himikat123/Simple-Clock-BIM32/Solidworks2023/buttons.png

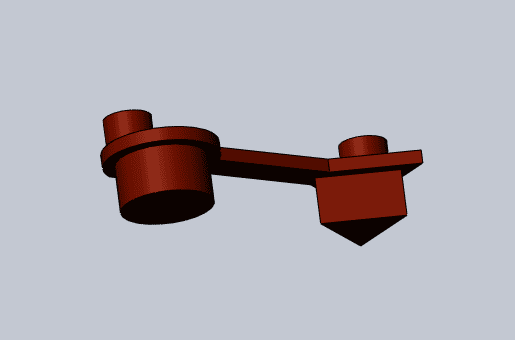
Solidworks2023/buttons.png
