himikat123/Simple-Clock-BIM32/Solidworks2023/cover.png

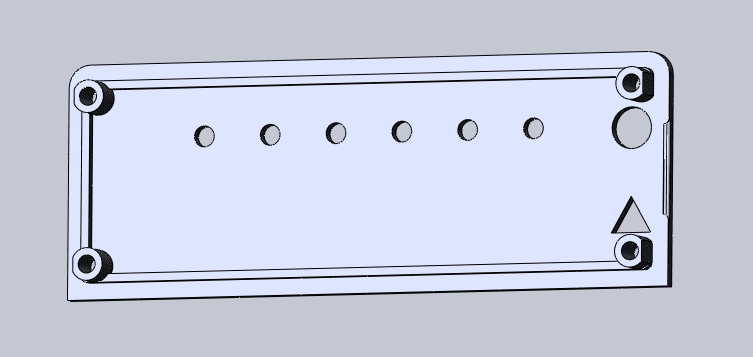
Solidworks2023/cover.png
