himikat123/Simple-Clock-BIM32/Solidworks2023/face.png

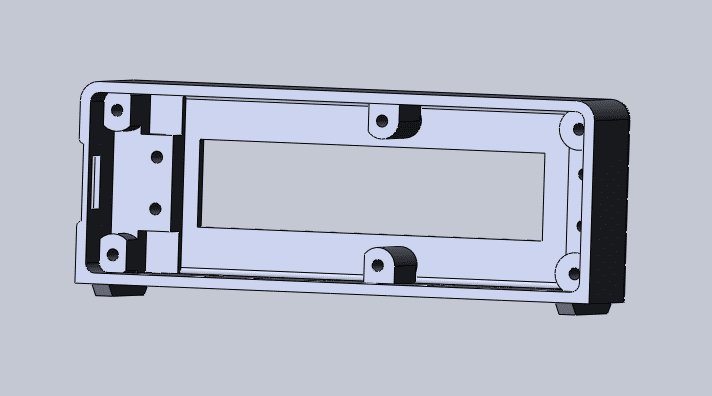
Solidworks2023/face.png
