himikat123/Simple-Clock-BIM32/STL/buttons.png

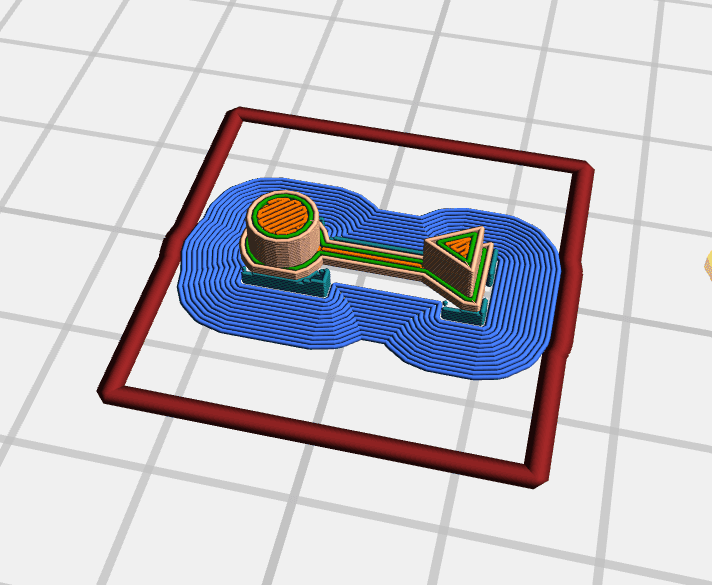
STL/buttons.png
