himikat123/Simple-Clock-BIM32/STL/cover.png

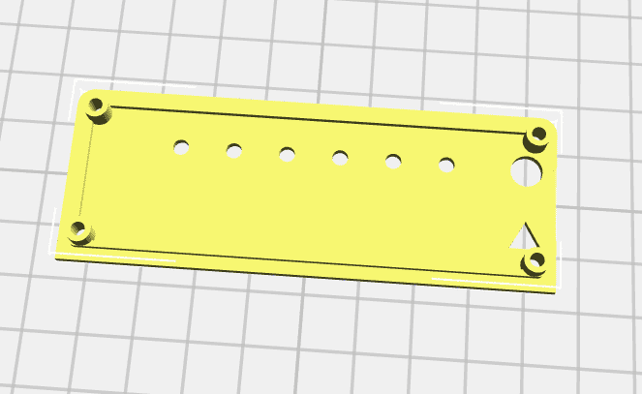
STL/cover.png
