himikat123/Simple-Clock-BIM32/STL/face.png

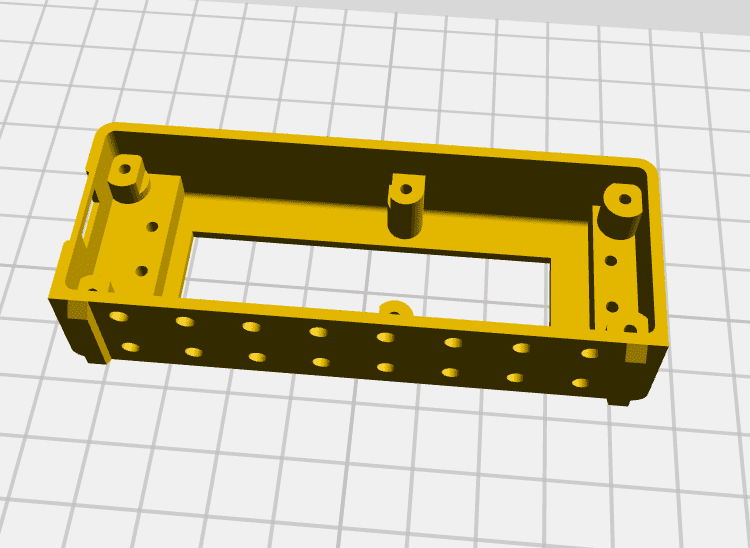
STL/face.png
