himikat123/Simple-Clock-BIM32/Solidworks2023/node mcu/esp1.SLDPRT

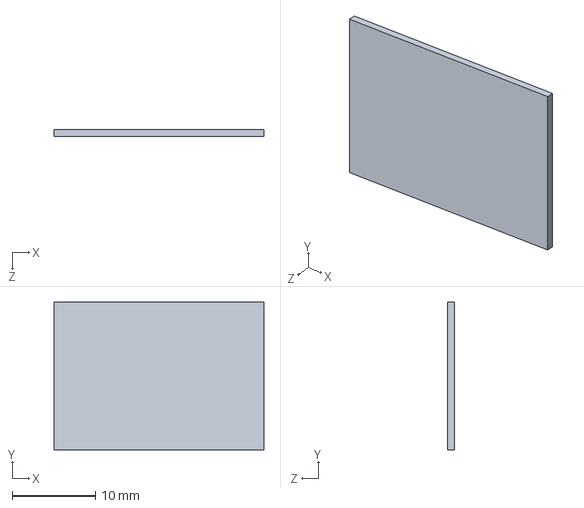
[picture p42: CAD file, 2024-11-11]
Solidworks2023/node mcu/esp1.SLDPRT
25.3 x 17.8 x 0.8 mm
